dkej123/zBox/assets/photos/admin-device.png

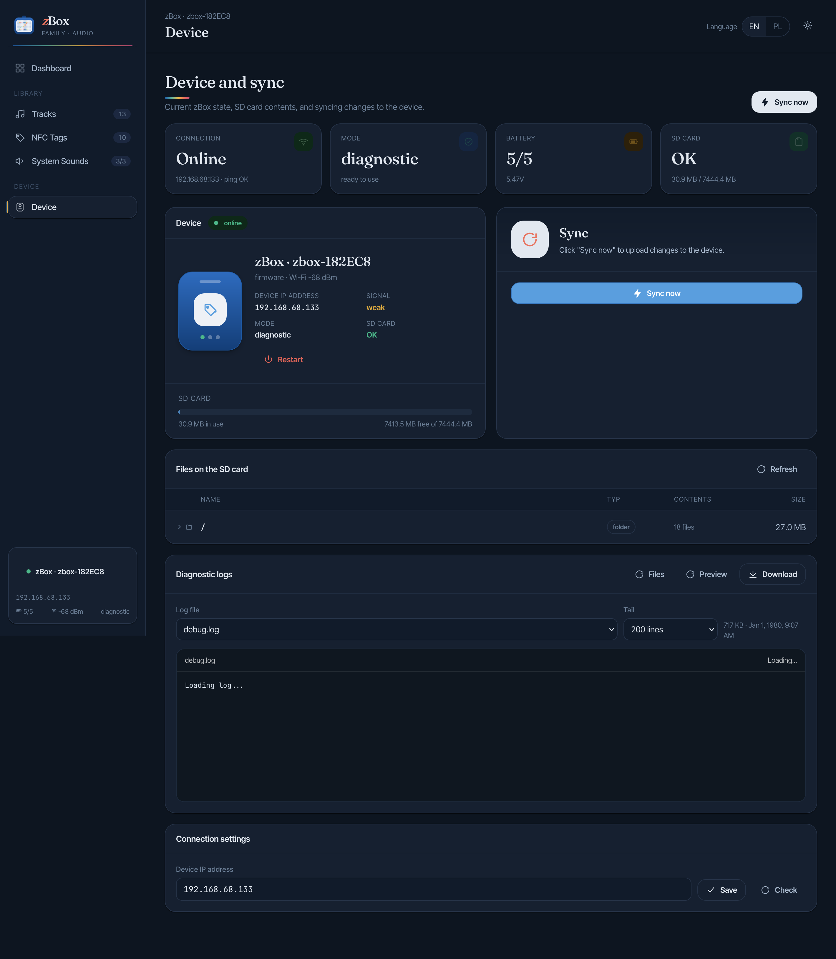
assets/photos/admin-device.png
