dkej123/zBox/assets/photos/admin-system-sounds.png

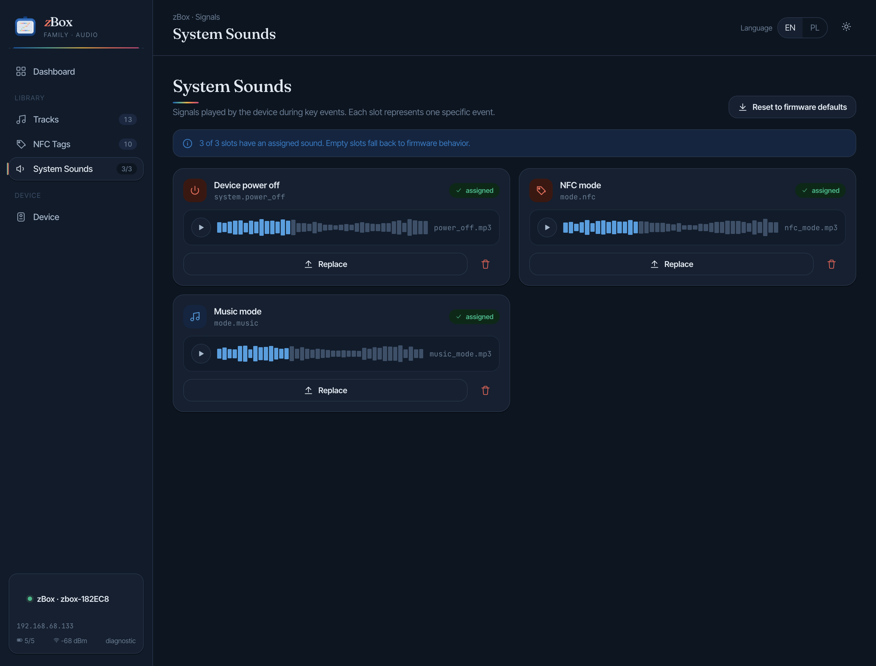
assets/photos/admin-system-sounds.png
