dkej123/zBox/cards_images/banan.png

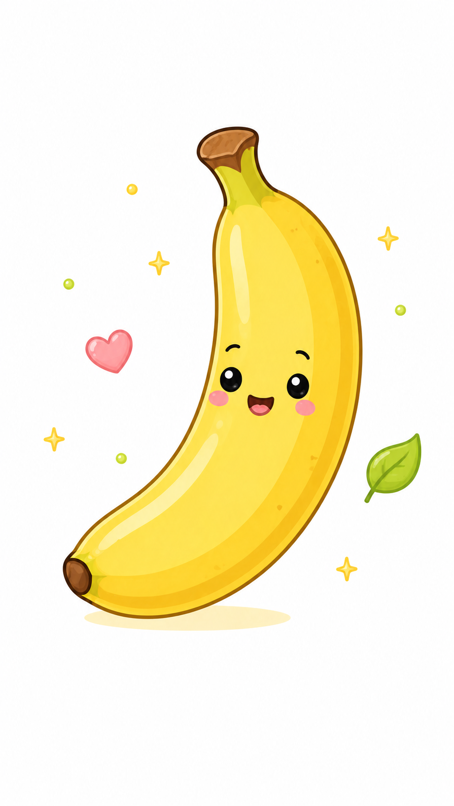
cards_images/banan.png
