dkej123/zBox/cards_images/beben.png

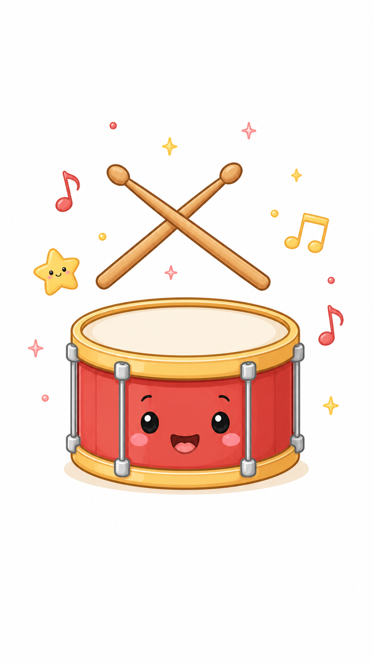
cards_images/beben.png
