dkej123/zBox/cards_images/chmurka.png

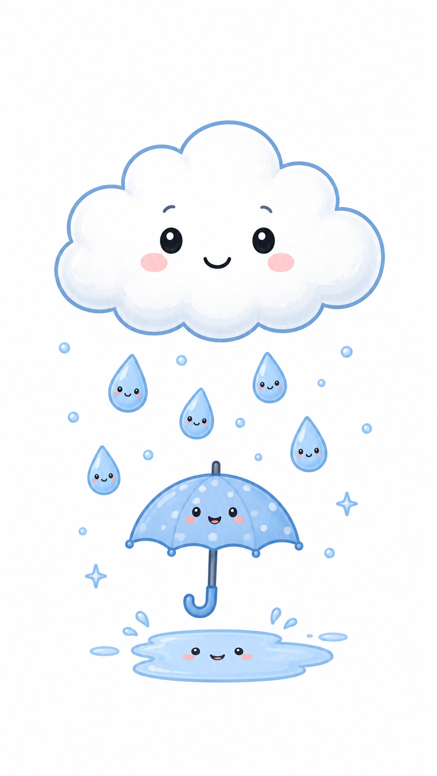
cards_images/chmurka.png
