dkej123/zBox/cards_images/domek.png

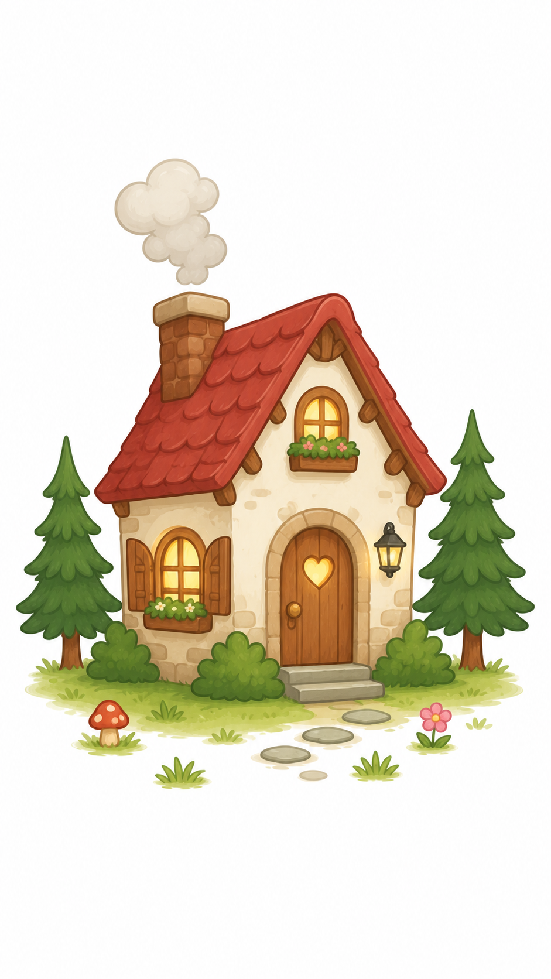
cards_images/domek.png
