dkej123/zBox/cards_images/drzewo.png

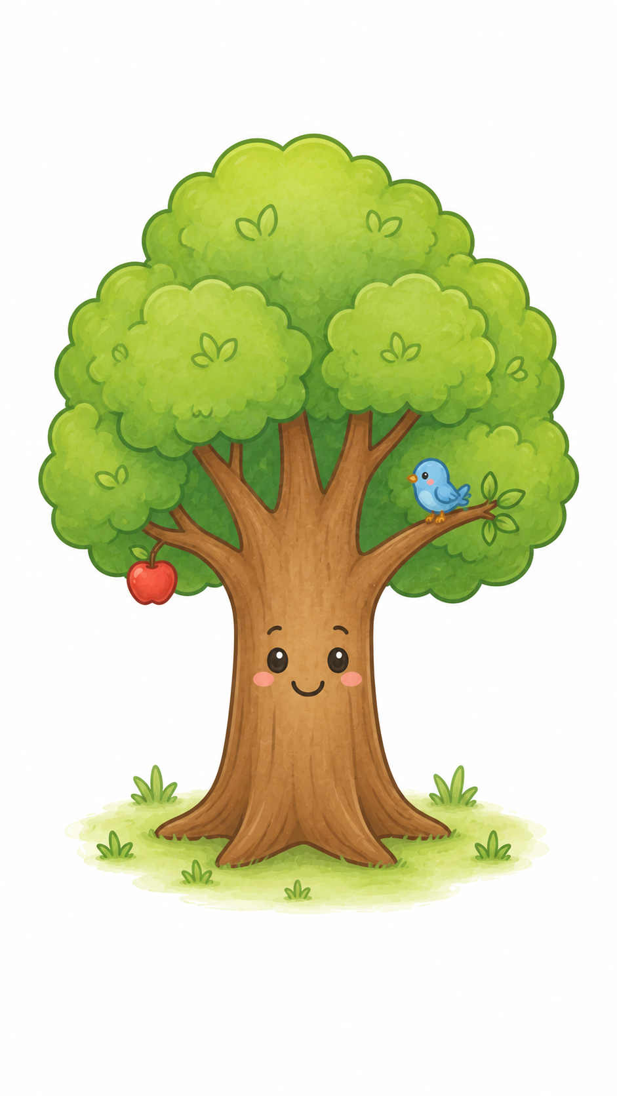
cards_images/drzewo.png
