dkej123/zBox/cards_images/gitara.png

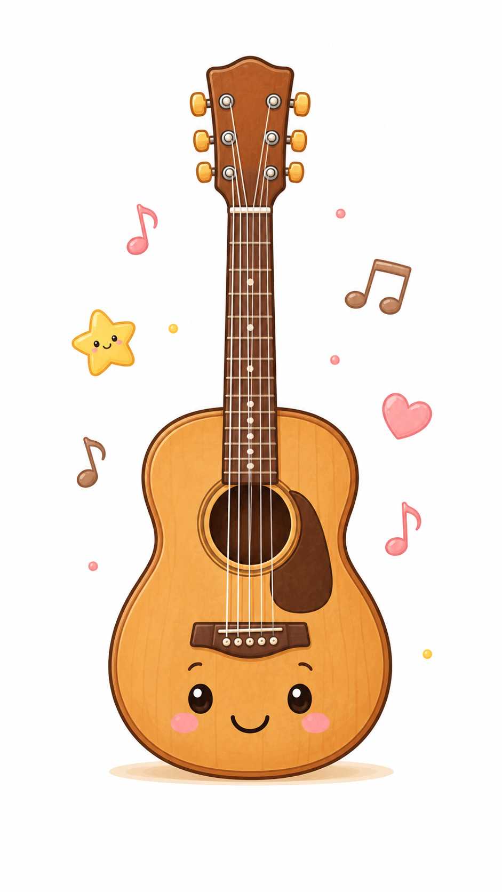
cards_images/gitara.png
