dkej123/zBox/cards_images/grzechotki.png

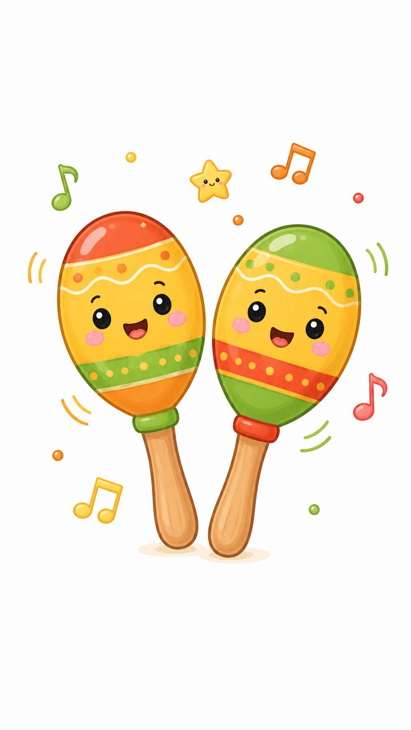
cards_images/grzechotki.png
