dkej123/zBox/cards_images/jablko.png

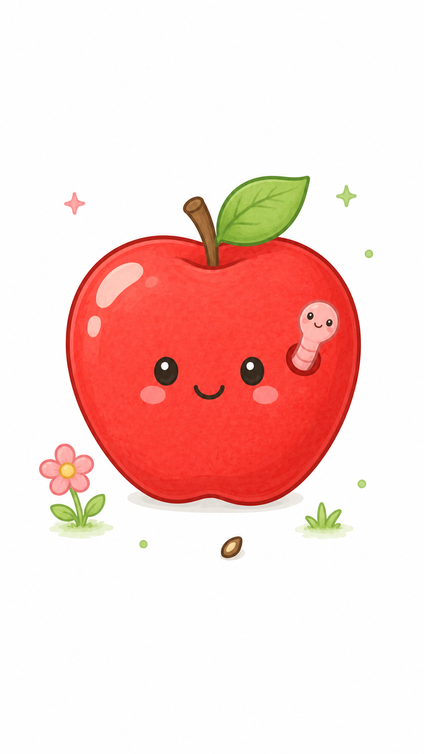
cards_images/jablko.png
