dkej123/zBox/cards_images/jednorozec.png

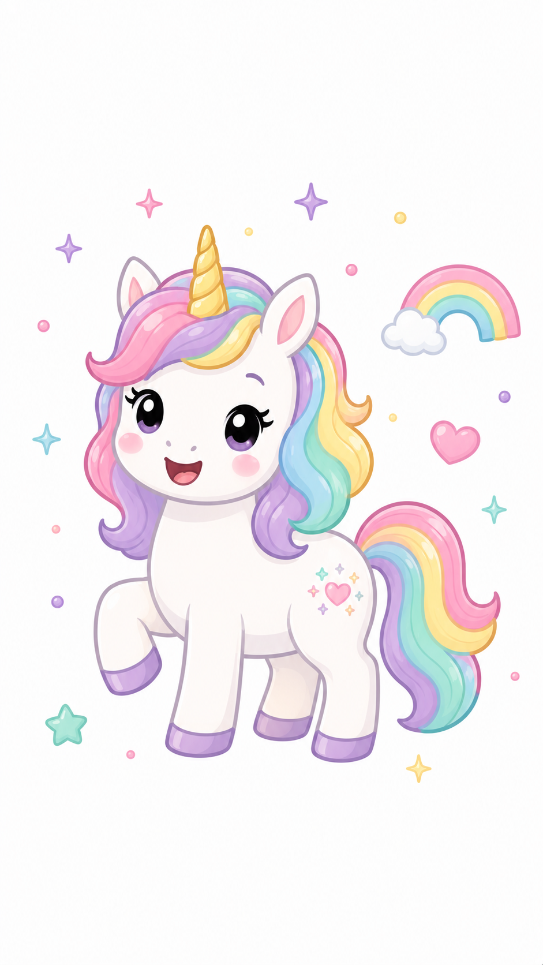
cards_images/jednorozec.png
