dkej123/zBox/cards_images/kometa.png

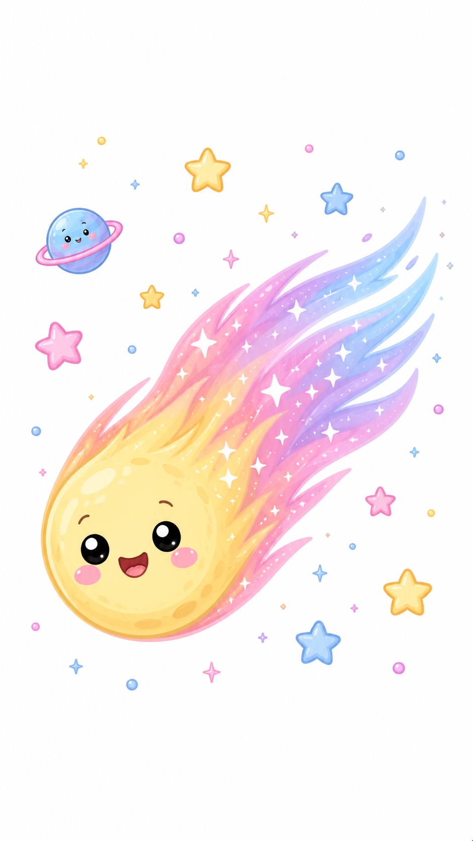
cards_images/kometa.png
