dkej123/zBox/cards_images/kosmita.png

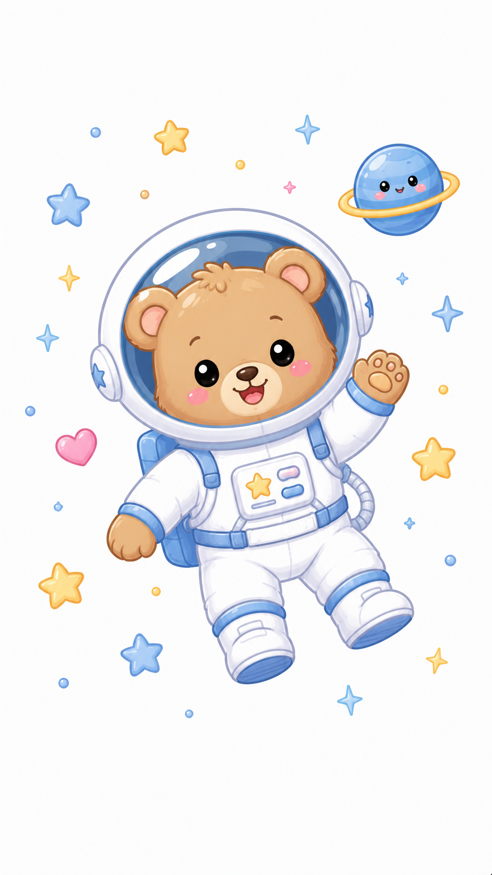
cards_images/kosmita.png
