dkej123/zBox/cards_images/krab.png

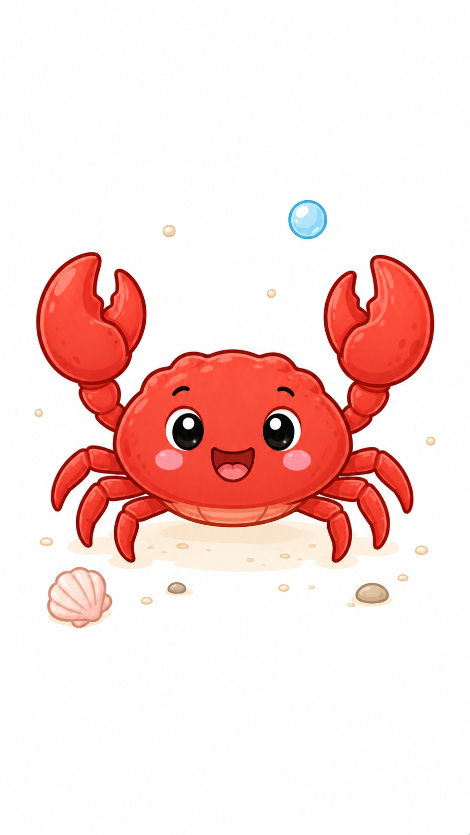
cards_images/krab.png
