dkej123/zBox/cards_images/ksiezyc.png

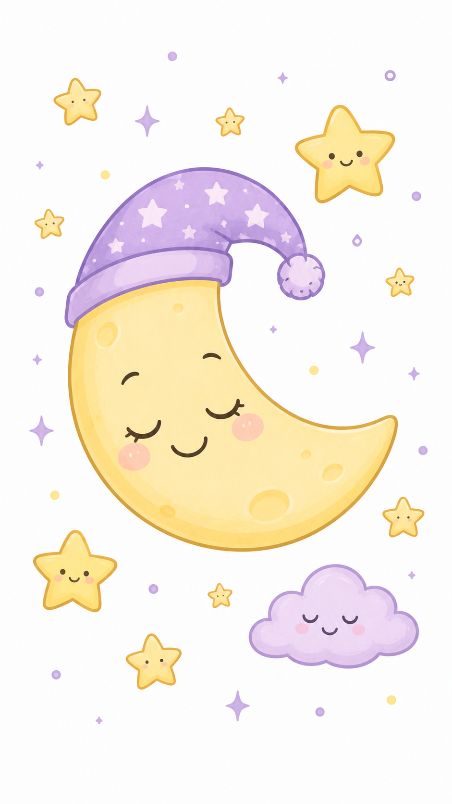
cards_images/ksiezyc.png
