dkej123/zBox/cards_images/kurczak.png

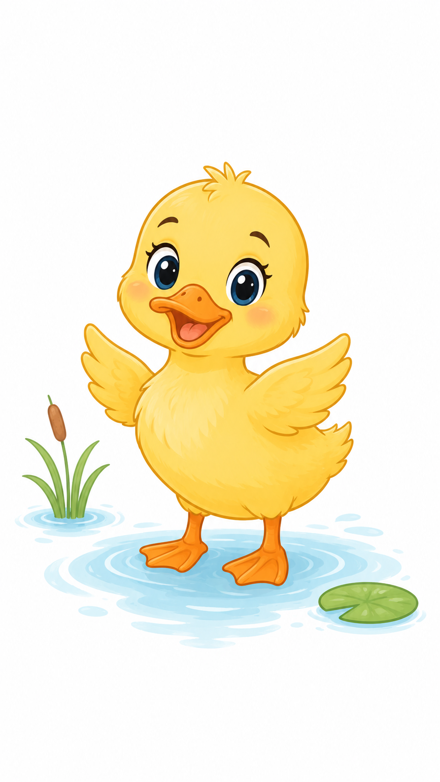
cards_images/kurczak.png
