dkej123/zBox/cards_images/lody.png

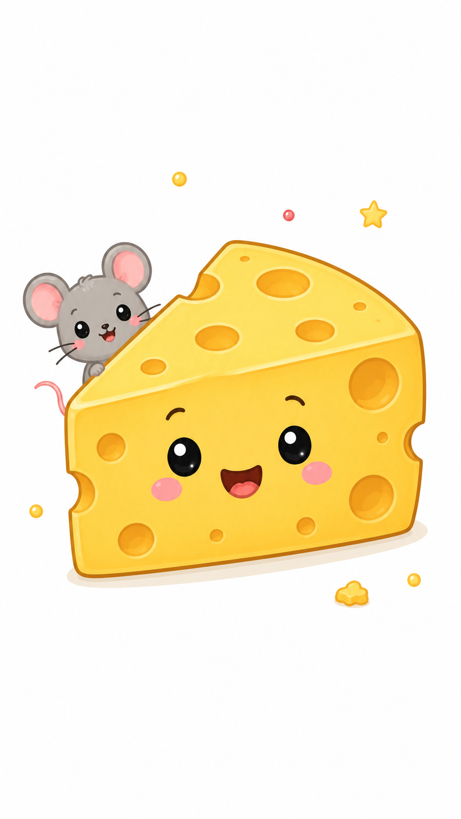
cards_images/lody.png
