dkej123/zBox/cards_images/lozko.png

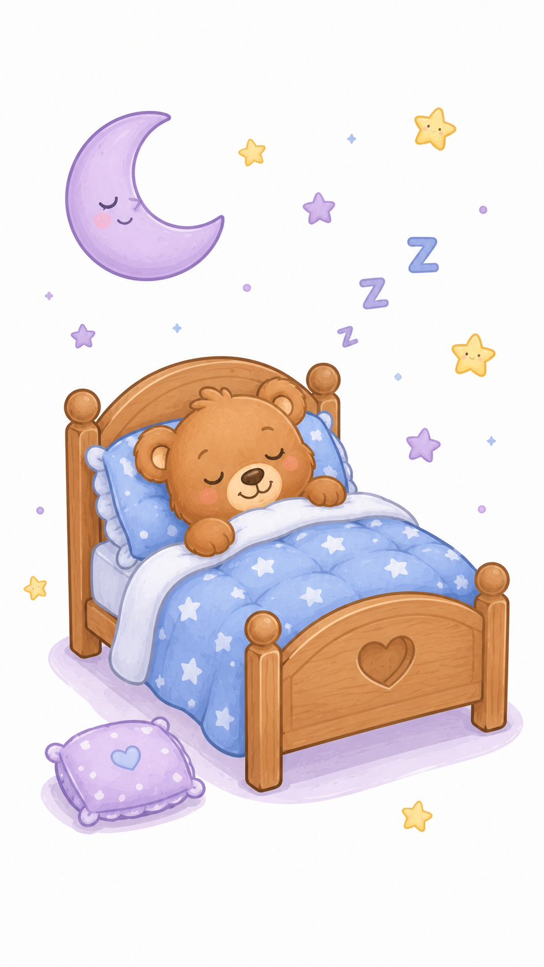
cards_images/lozko.png
