dkej123/zBox/cards_images/malpa.png

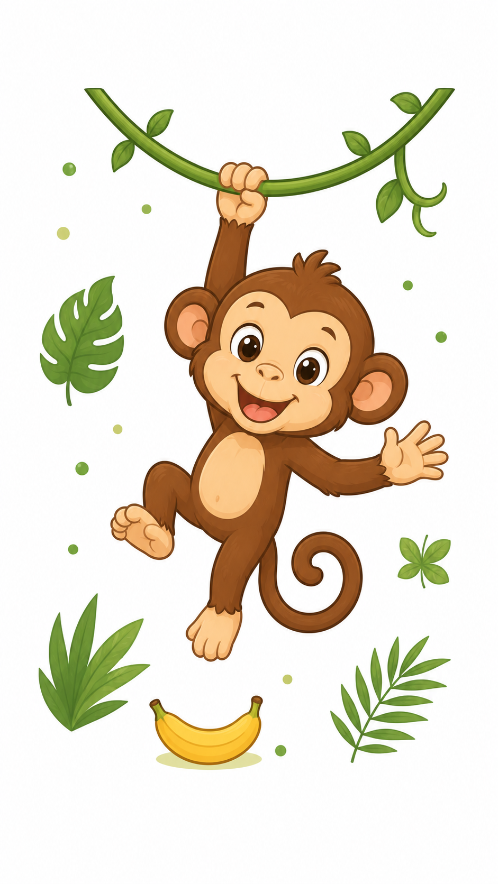
cards_images/malpa.png
