dkej123/zBox/cards_images/marchewka.png

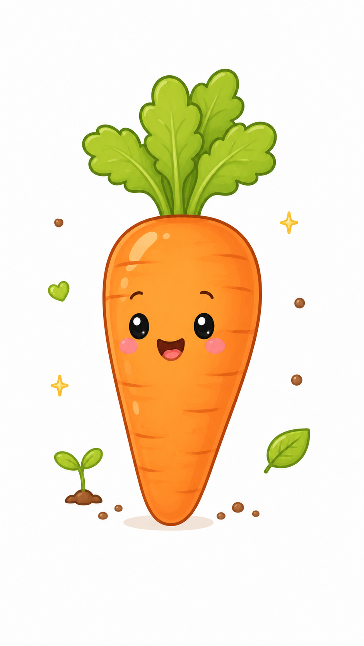
cards_images/marchewka.png
