dkej123/zBox/cards_images/osiornica.png

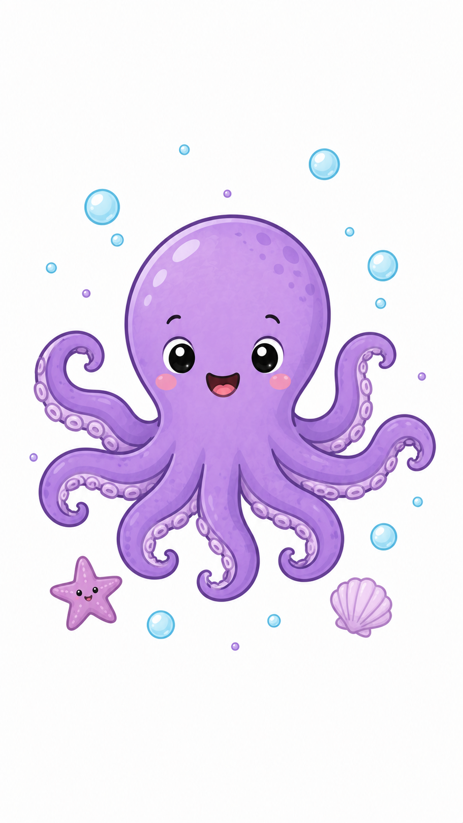
cards_images/osiornica.png
