dkej123/zBox/cards_images/panda.png

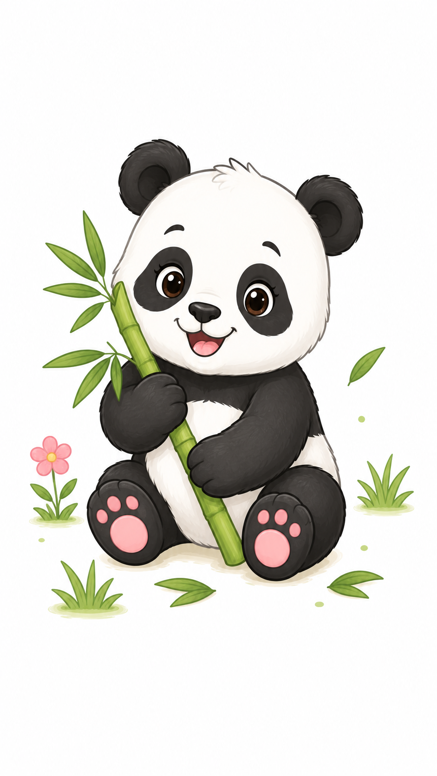
cards_images/panda.png
