dkej123/zBox/cards_images/pianino.png

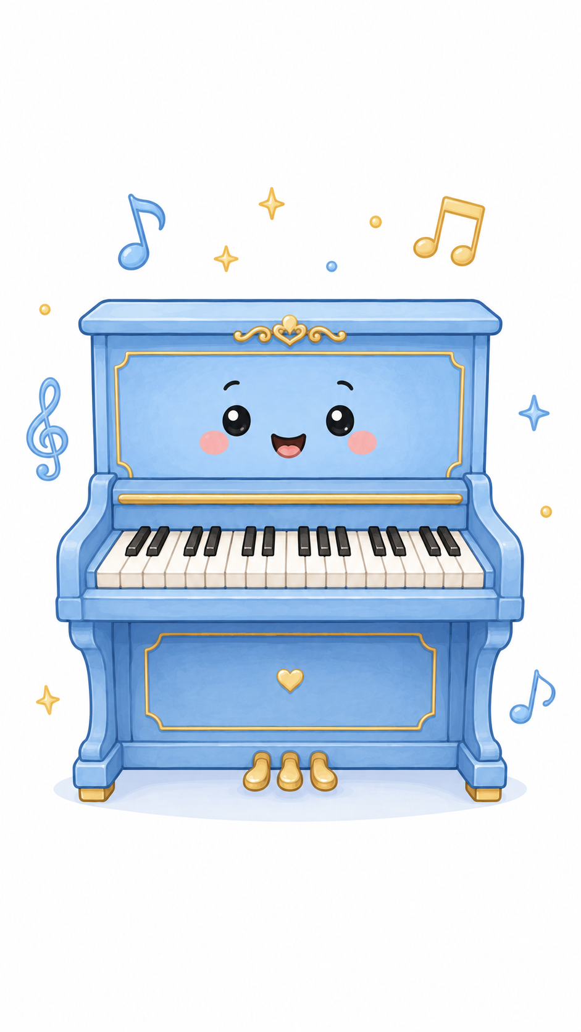
cards_images/pianino.png
