dkej123/zBox/cards_images/pies.png

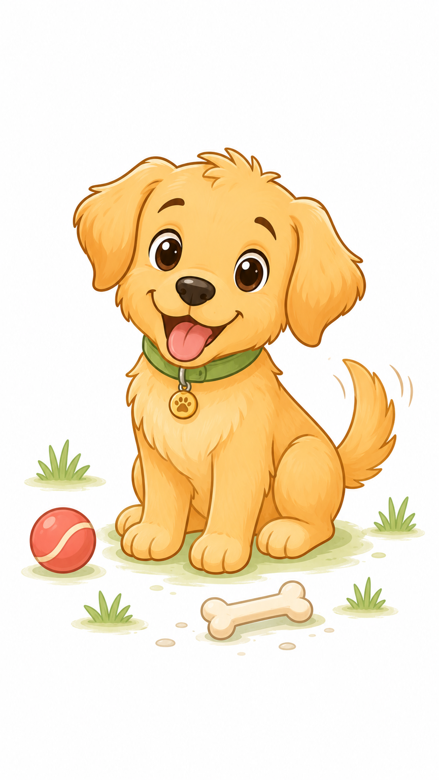
cards_images/pies.png
