dkej123/zBox/cards_images/pociag.png

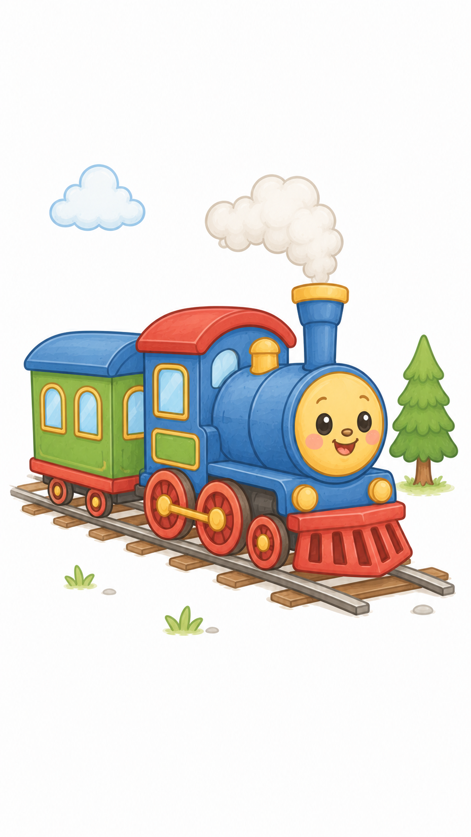
cards_images/pociag.png
