dkej123/zBox/cards_images/rybka.png

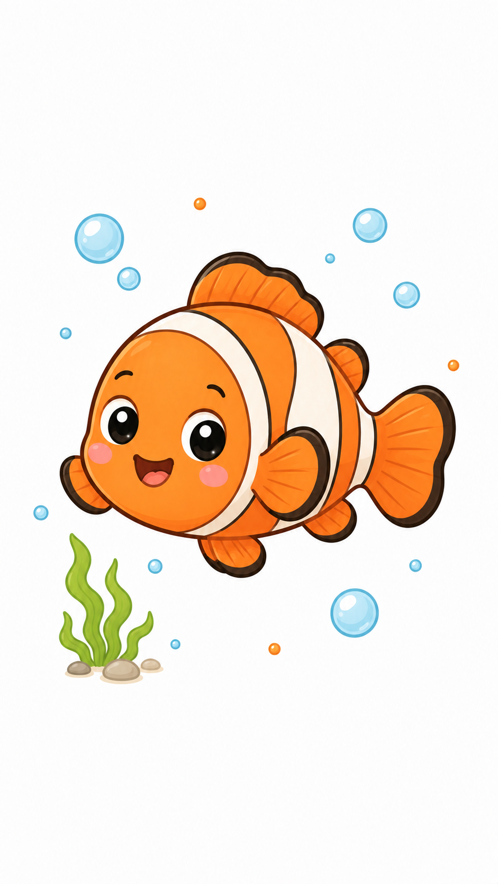
cards_images/rybka.png
