dkej123/zBox/cards_images/samochod.png

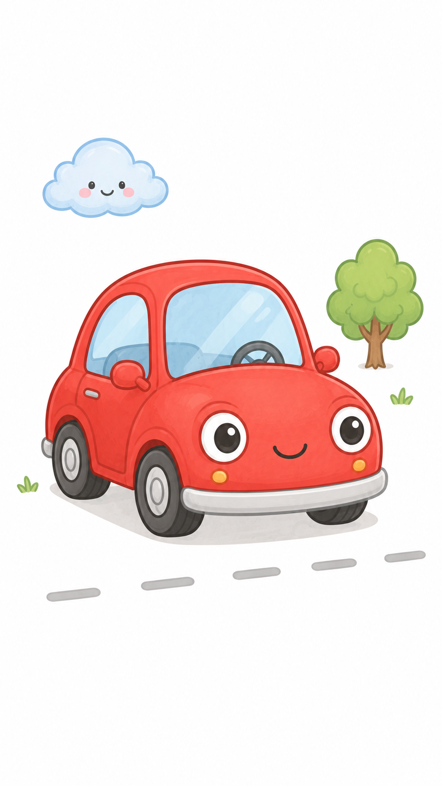
cards_images/samochod.png
