dkej123/zBox/cards_images/slon.png

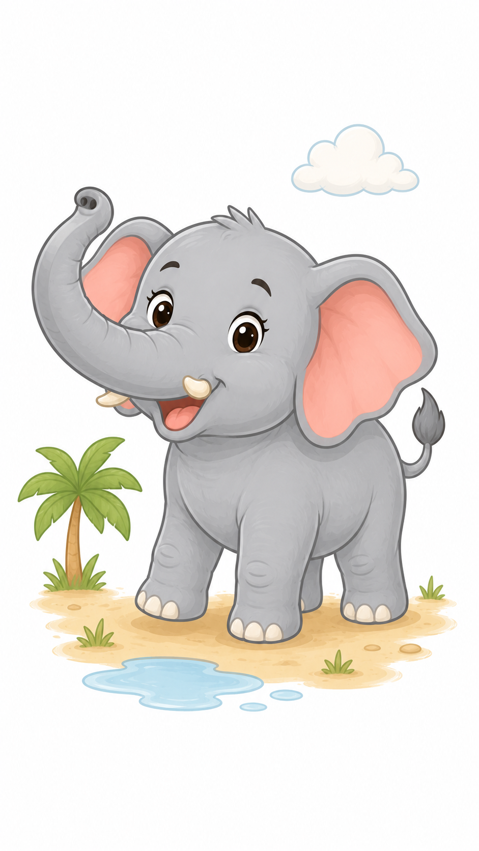
cards_images/slon.png
