dkej123/zBox/cards_images/smok.png

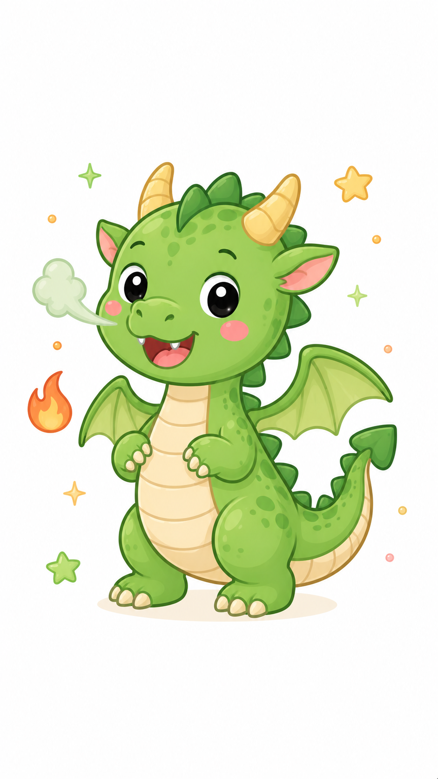
cards_images/smok.png
