dkej123/zBox/cards_images/straz.png

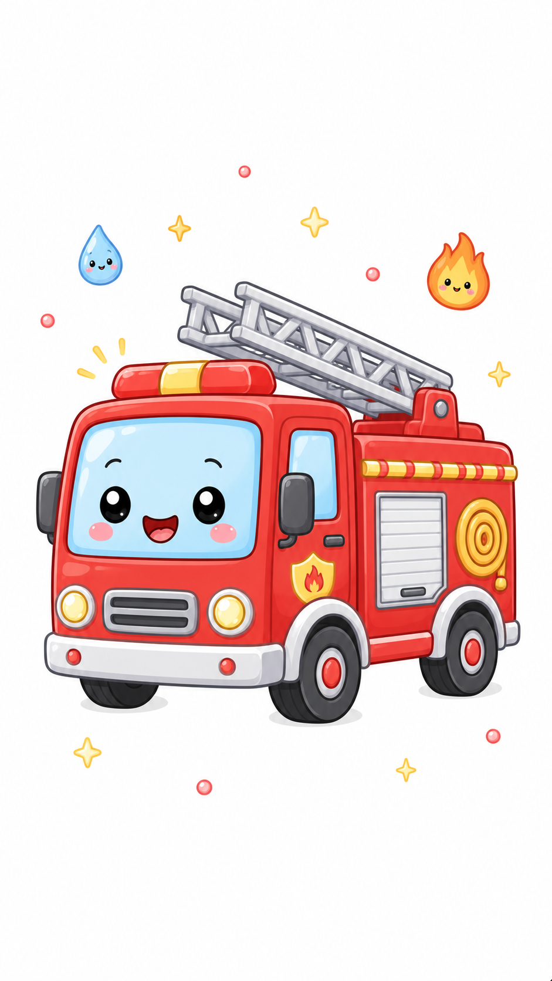
cards_images/straz.png
