dkej123/zBox/cards_images/tecza.png

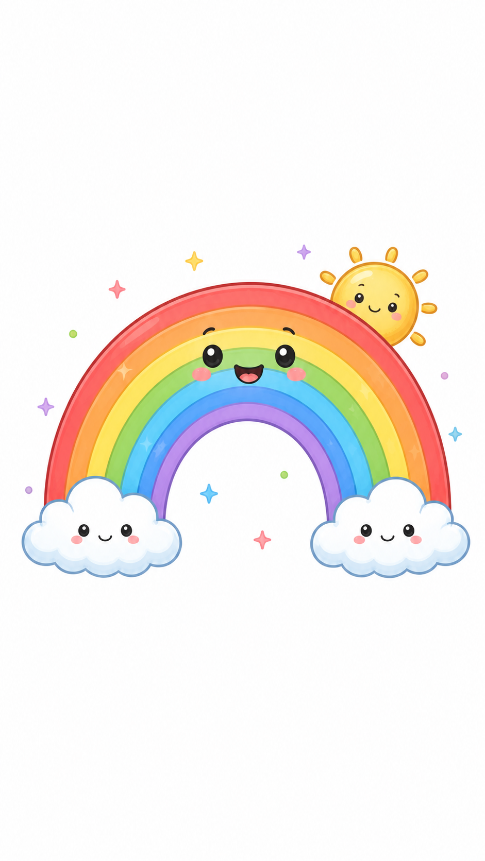
cards_images/tecza.png
