dkej123/zBox/cards_images/tosty.png

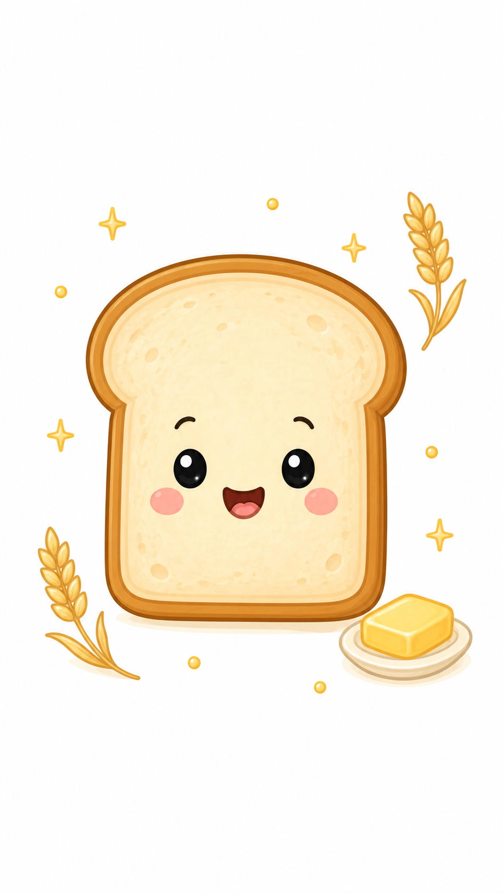
cards_images/tosty.png
