dkej123/zBox/cards_images/trabka.png

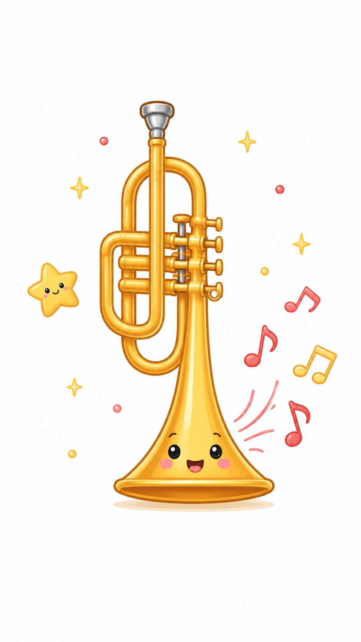
cards_images/trabka.png
