dkej123/zBox/cards_images/traktor.png

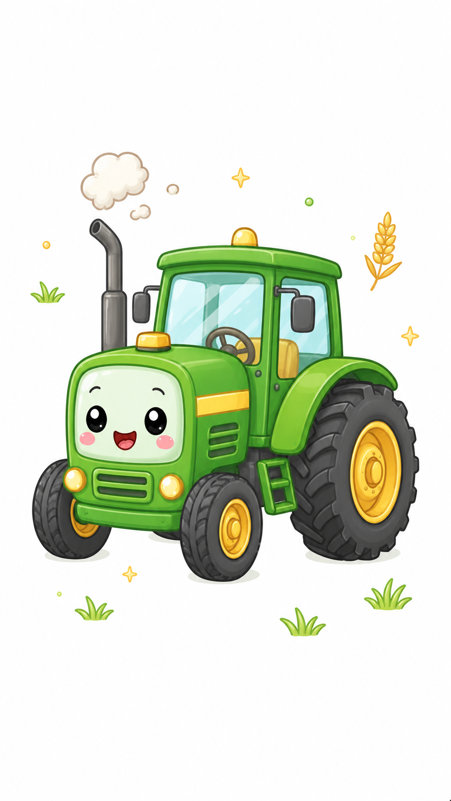
cards_images/traktor.png
