dkej123/zBox/cards_images/ufo.png

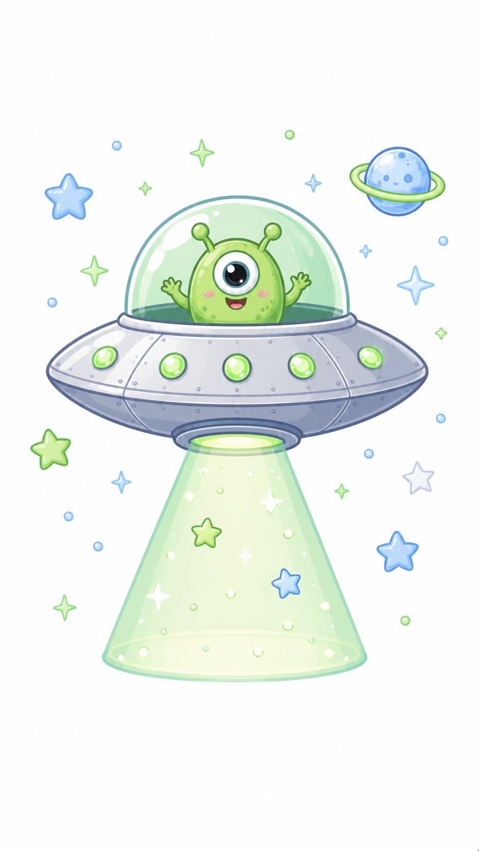
cards_images/ufo.png
