dkej123/zBox/cards_images/wieloryb.png

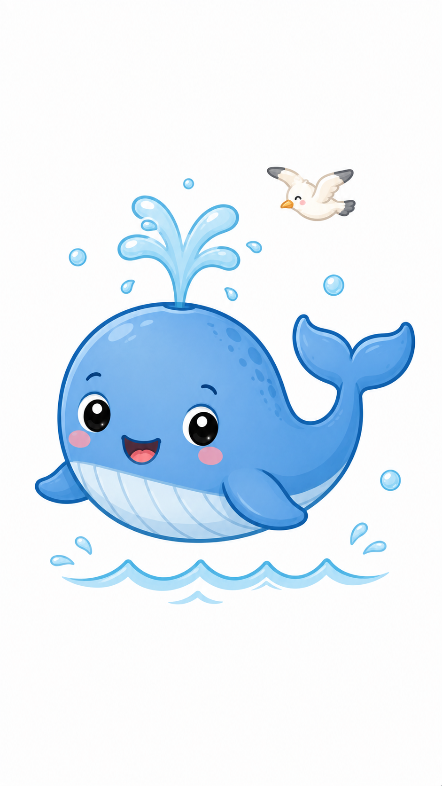
cards_images/wieloryb.png
