dkej123/zBox/cards_images/wrozka.png

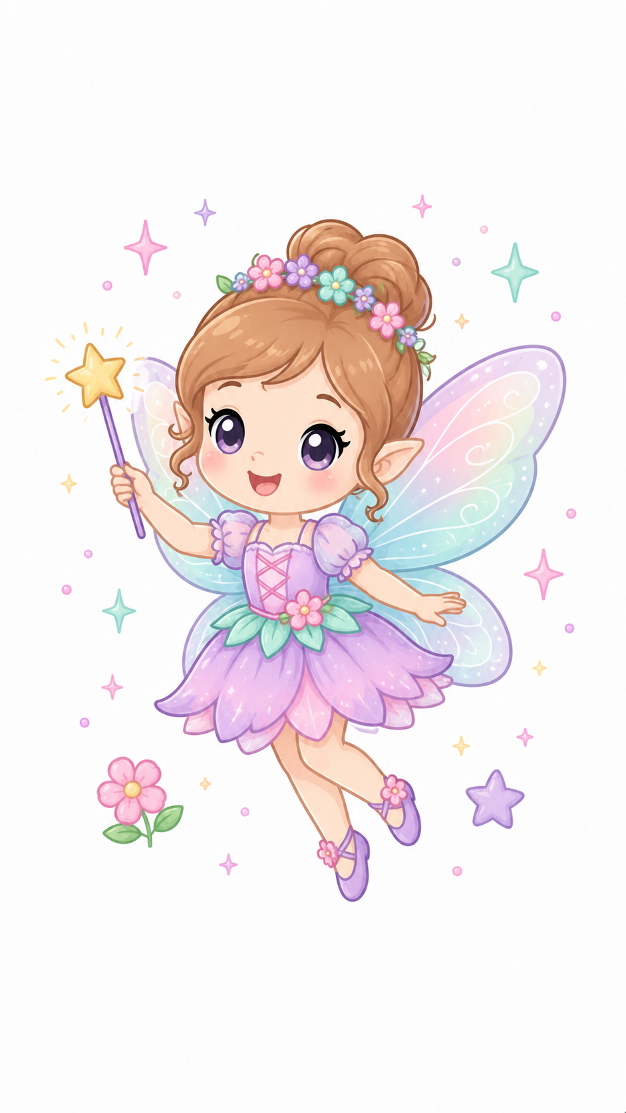
cards_images/wrozka.png
