dkej123/zBox/cards_images/zaglowka.png

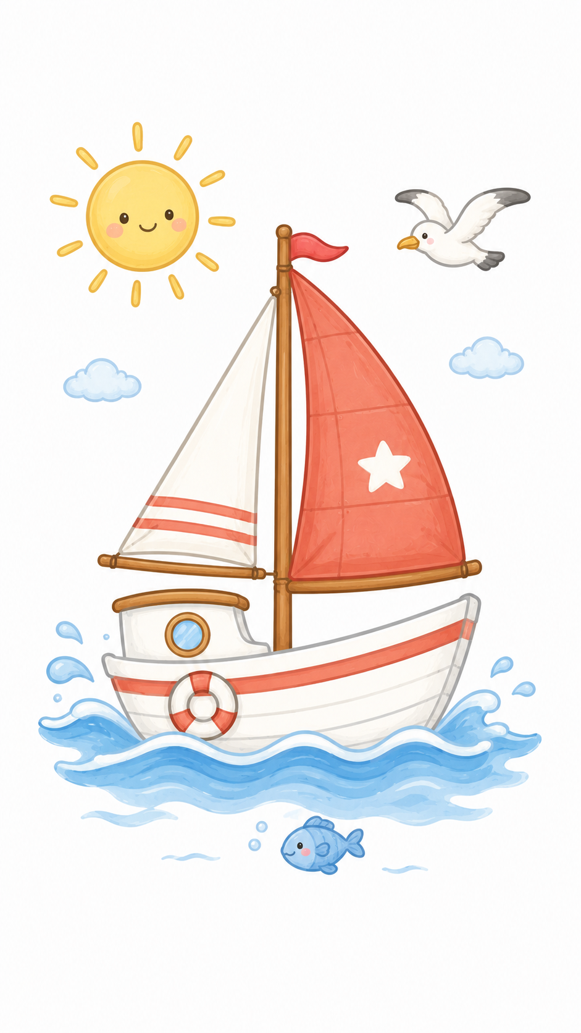
cards_images/zaglowka.png
