dkej123/zBox/cards_images/zolw.png

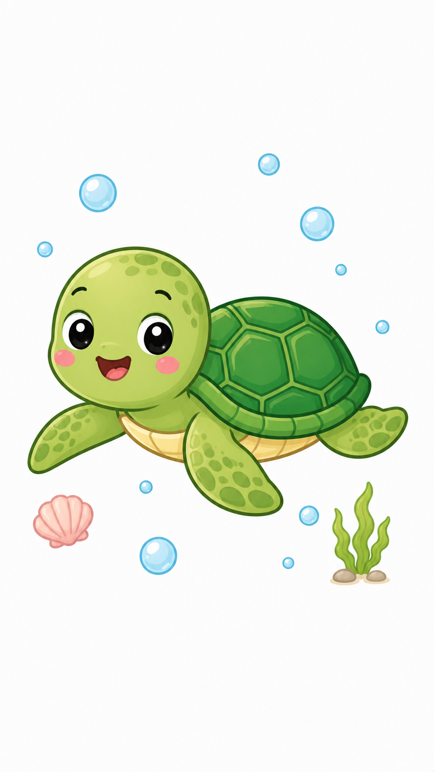
cards_images/zolw.png
