dkej123/zBox/cards_images/zyrafa.png

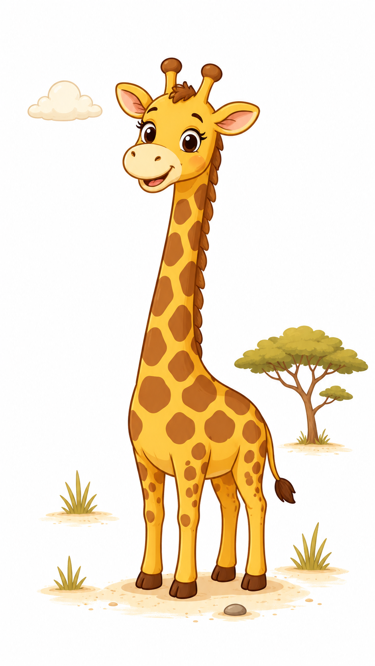
cards_images/zyrafa.png
